hmsmart/air-cleaners/cr_boxes/three_by_three/20x20x1_5F/center_left.3mf

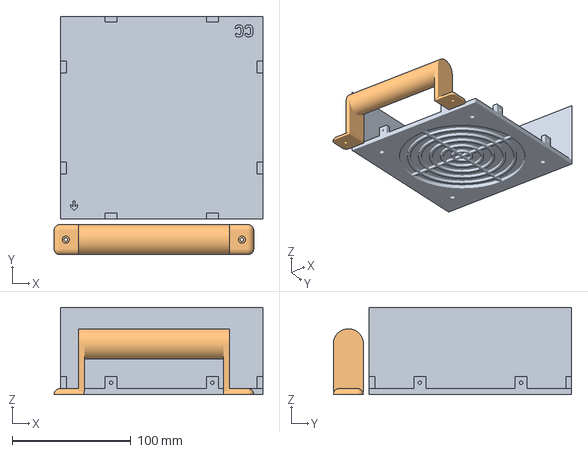
[picture p15: CAD file, 2025-09-12]
cr_boxes/three_by_three/20x20x1_5F/center_left.3mf
176.1 x 200.9 x 73.4 mm
center_center.stl
40tall_handle.stl
