hmsmart/air-cleaners/laminair/3mf_files/stand.3mf

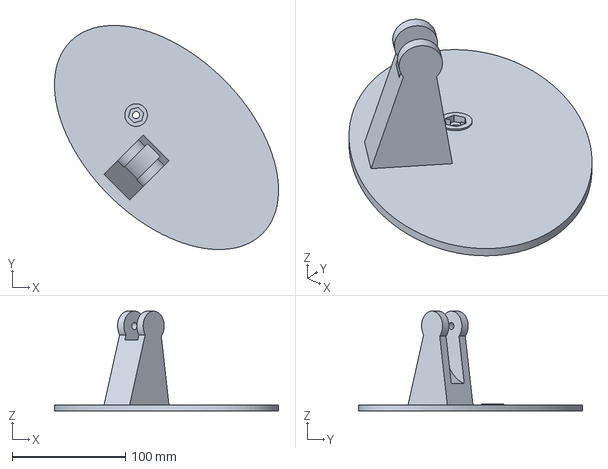
[picture p16: CAD file, 2025-09-12]
laminair/3mf_files/stand.3mf
197.8 x 197.8 x 88.1 mm
