hmsmart/air-cleaners/cr_boxes/three_by_three/20x20x1_5F/69tall_handle.stl

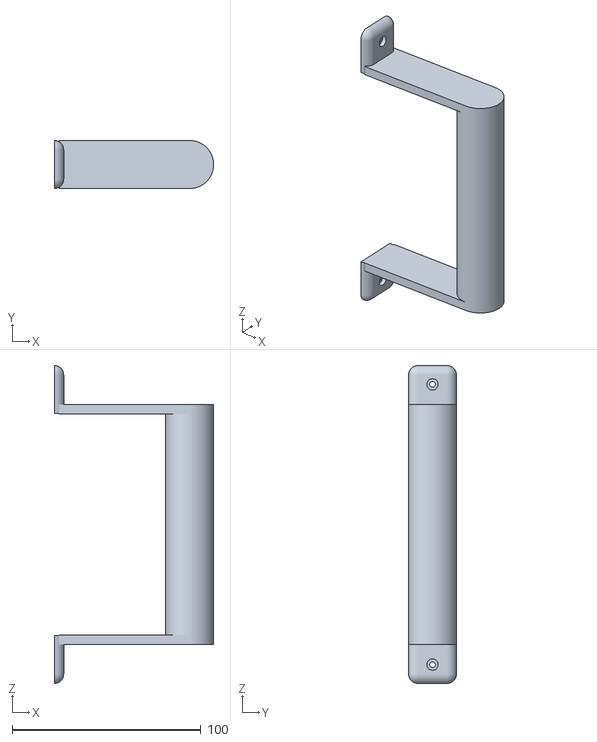
[picture p17: CAD file, 2025-09-12]
cr_boxes/three_by_three/20x20x1_5F/69tall_handle.stl
84.4 x 25.4 x 168.4
