hmsmart/air-cleaners/laminair/3mf_files/power_switch_2.3mf

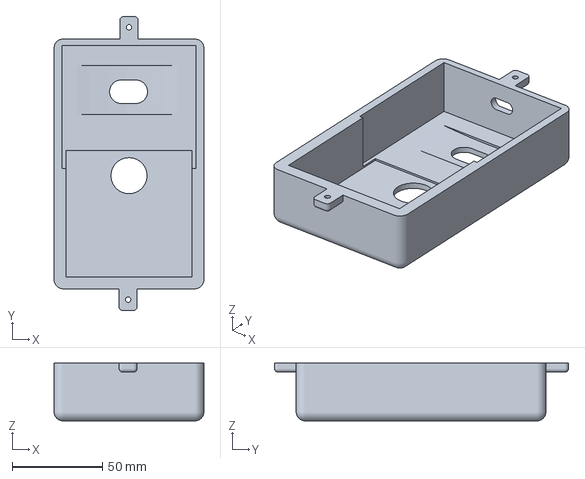
[picture p18: CAD file, 2025-09-12]
laminair/3mf_files/power_switch_2.3mf
83.0 x 162.9 x 32.0 mm
